forsslund/hbits/src/hapticeffects.h

struct HapticStep {
    uint8_t amplitude; // 0-255
    uint16_t delayMs;  // hur länge denna amplitude ska spelas
};

using HapticEffect = std::vector<HapticStep>;
const HapticEffect EFFECT_CONST_VIBE = {
  {127, 10}
};

const HapticEffect EFFECT_PULSE_PURR = {
  {77, 5},
  {94, 5},
  {107, 5},
  {111, 5},
  {111, 5},
  {111, 5},
  {110, 5},
  {93, 5},
  {86, 5},
  {103, 5},
  {96, 5},
  {94, 5},
  {94, 5},
  {118, 5},
  {126, 5},
  {121, 5},
  {100, 5},
  {87, 5},
  {92, 5},
  {107, 5},
  {89, 5},
  {59, 5},
  {65, 5},
  {87, 5},
  {117, 5},
  {99, 5},
  {92, 5},
  {81, 5},
  {70, 5},
  {65, 5},
  {51, 5},
  {55, 5},
  {70, 5},
  {90, 5},
  {116, 5},
  {105, 5},
  {97, 5},
  {71, 5},
  {63, 5},
  {57, 5},
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
};

const HapticEffect EFFECT_AUDIO_NOISE = {
  {83, 5},
  {73, 5},
  {76, 5},
  {87, 5},
  {88, 5},
  {96, 5},
  {113, 5},
  {121, 5},
  {121, 5},
  {121, 5},
  {127, 5},
  {127, 5},
  {124, 5},
  {119, 5},
  {118, 5},
  {118, 5},
  {118, 5},
  {121, 5},
  {116, 5},
  {104, 5},
  {101, 5},
  {101, 5},
  {101, 5},
  {104, 5},
  {98, 5},
  {101, 5},
  {101, 5},
  {83, 5},
  {89, 5},
  {91, 5},
  {72, 5},
  {62, 5},
  {79, 5},
  {68, 5},
  {84, 5},
  {104, 5},
  {106, 5},
  {96, 5},
  {100, 5},
  {100, 5},
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
};

const HapticEffect EFFECT_WAVE = {
  {0, 1},
  {20, 1},
  {40, 1},
  {60, 1},
  {80, 1},
  {100, 1},
  {120, 1},
  {127, 1},
  {120, 1},
  {100, 1},
  {80, 1},
  {60, 1},
  {40, 1},
  {20, 1}
};

const HapticEffect EFFECT_BRADYCARDIA_HEAVY = {
  {40, 60},
  {0, 30},
  {25, 40},
  {127, 70},
  {20, 50},
  {0, 120},
  {60, 120},
  {30, 140},
  {0, 600}
};

const HapticEffect EFFECT_STRONG_BUZZ = {
  {0, 10},
  {18, 10},
  {18, 10},
  {18, 10},
  {18, 10},
  {18, 10},
  {18, 10},
  {36, 10},
  {36, 10},
  {36, 10},
  {36, 10},
  {36, 10},
  {36, 10},
  {126, 10},
  {126, 10},
  {126, 10},
  {126, 10},
  {126, 10},
  {126, 10},
  {126, 10},
  {126, 10},
  {36, 10},
  {36, 10},
  {36, 10},
  {36, 10},
  {36, 10},
  {36, 10},
  {18, 10},
  {18, 10},
  {18, 10},
  {18, 10},
  {18, 10},
  {18, 10},
};
